Cinnnnnnndy/wall-planter/files/front.png

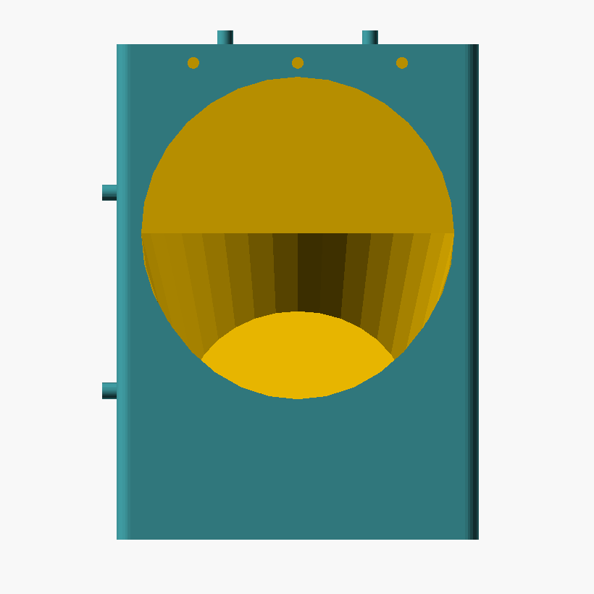
files/front.png
