Cinnnnnnndy/wall-planter/files/preview.png

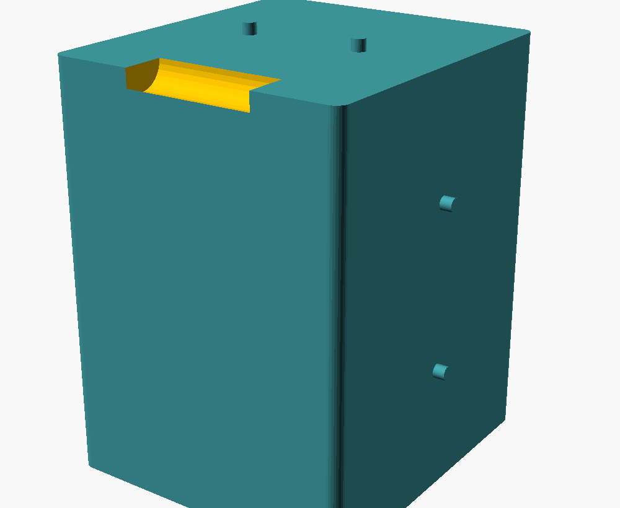
files/preview.png
