Cinnnnnnndy/wall-planter/files/side.png

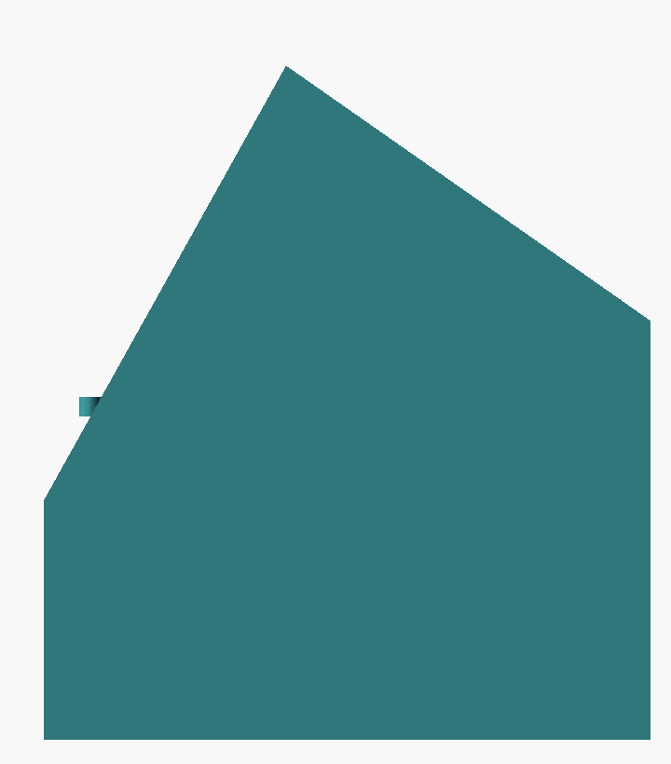
files/side.png
