Cinnnnnnndy/wall-planter/filesv2/v4_back.png

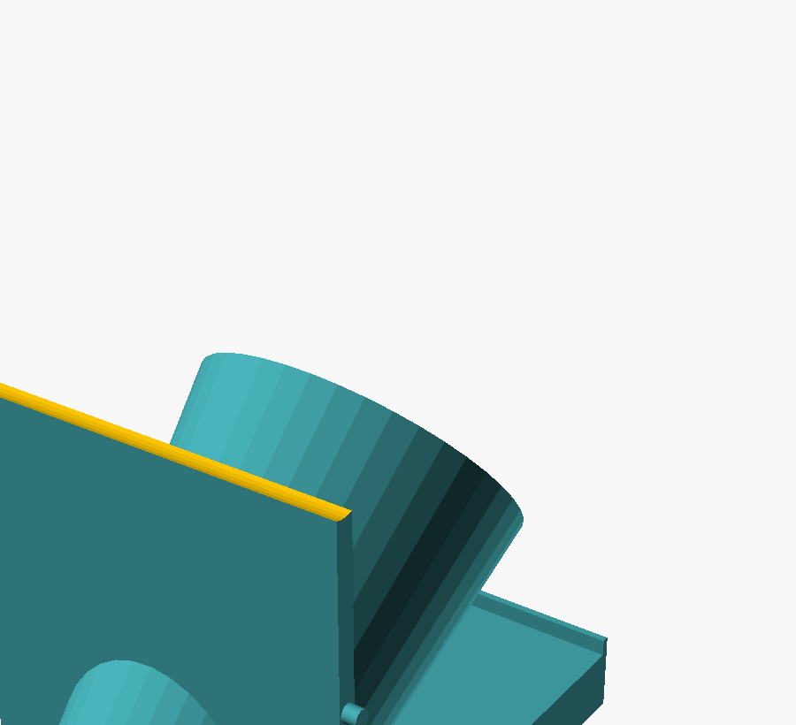
filesv2/v4_back.png
