Cinnnnnnndy/wall-planter/filesv2/v4_hero.png

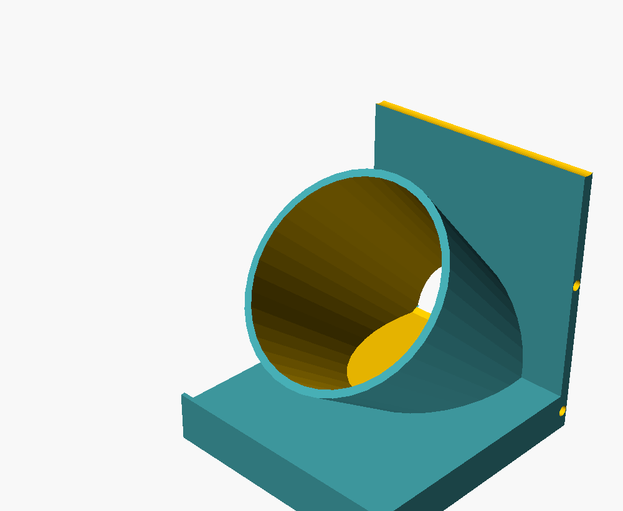
filesv2/v4_hero.png
