Cinnnnnnndy/wall-planter/filesv2/v4_ventcut.png

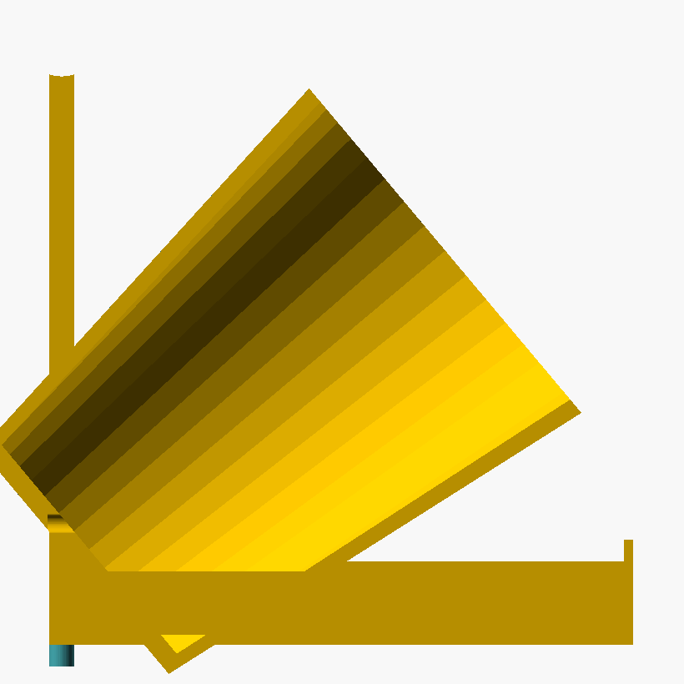
filesv2/v4_ventcut.png
